ytr0221/BHA_Stirrer/Pictures/20160302_161547.jpg

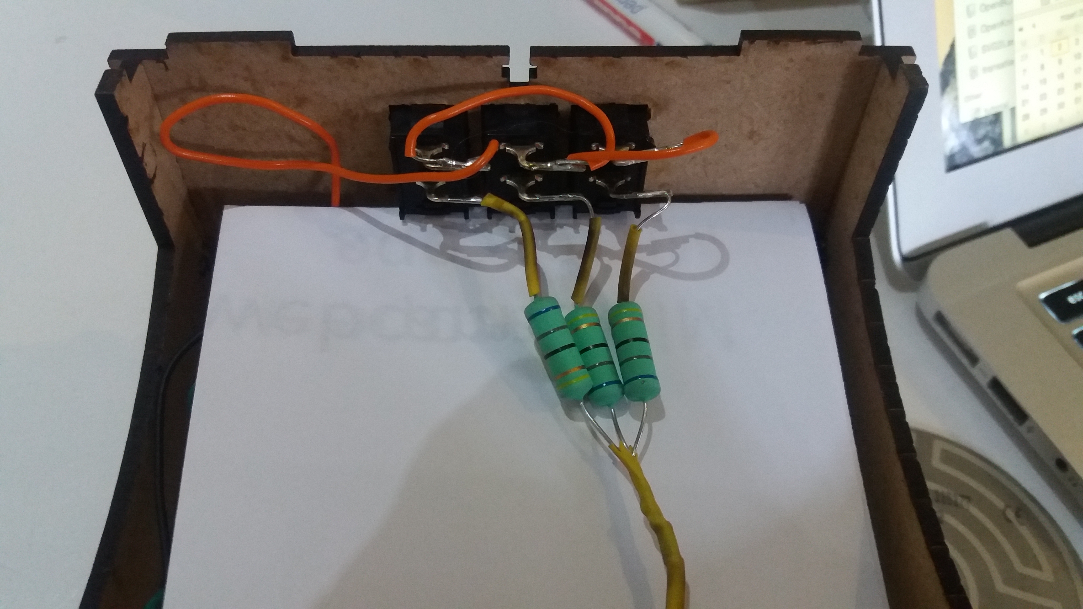
Pictures/20160302_161547.jpg
