ytr0221/BHA_Stirrer/Pictures/DSC_1296.JPG

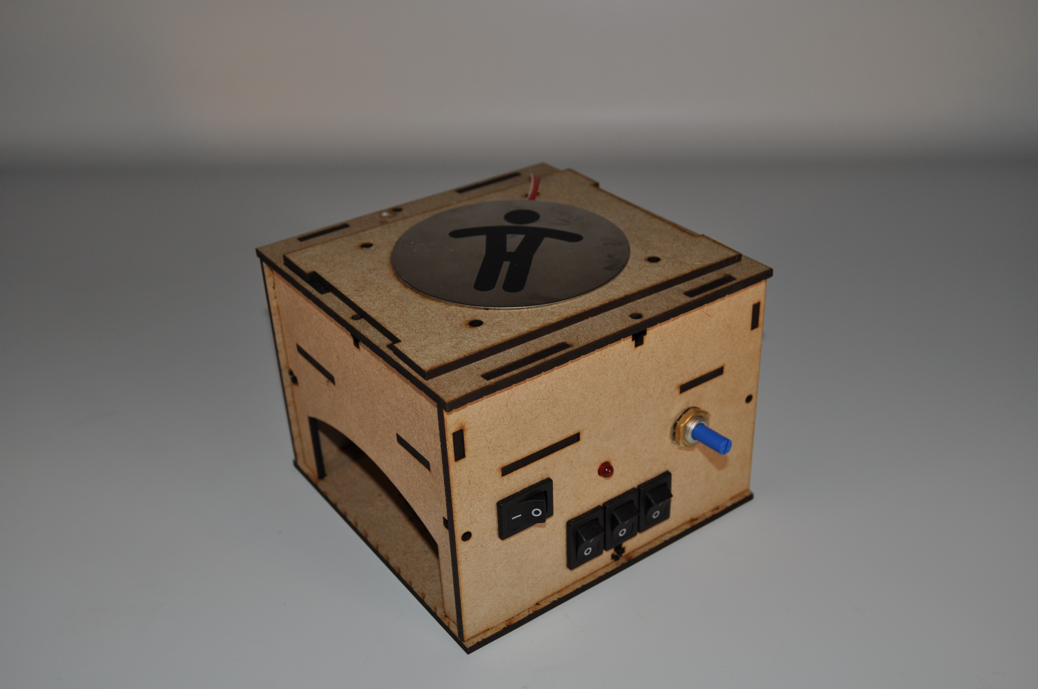
Pictures/DSC_1296.JPG
