ytr0221/BHA_Stirrer/Pictures/DSC_1297.JPG

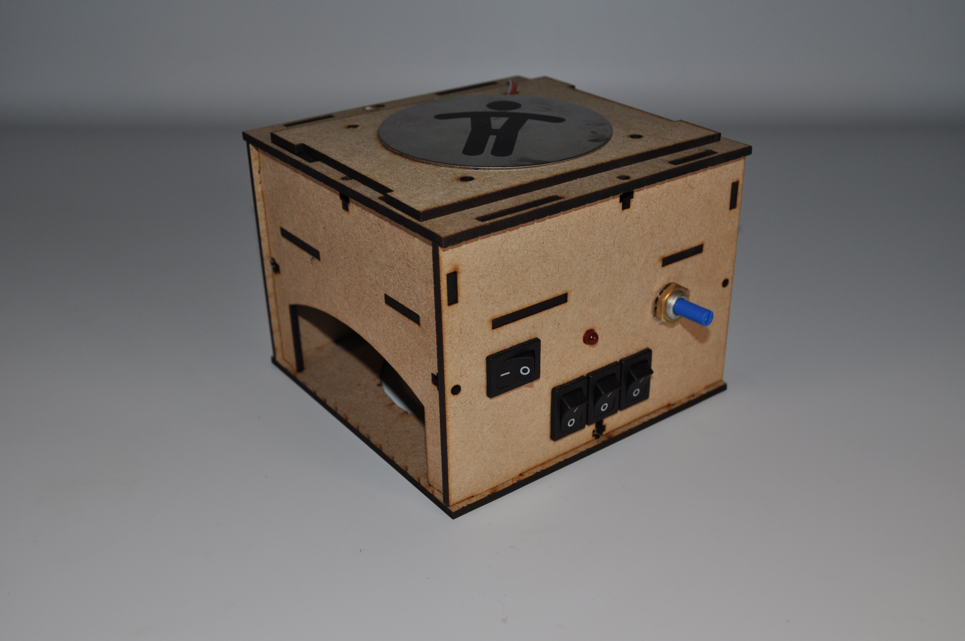
Pictures/DSC_1297.JPG
