ytr0221/BHA_Stirrer/Pictures/DSC_1299.JPG

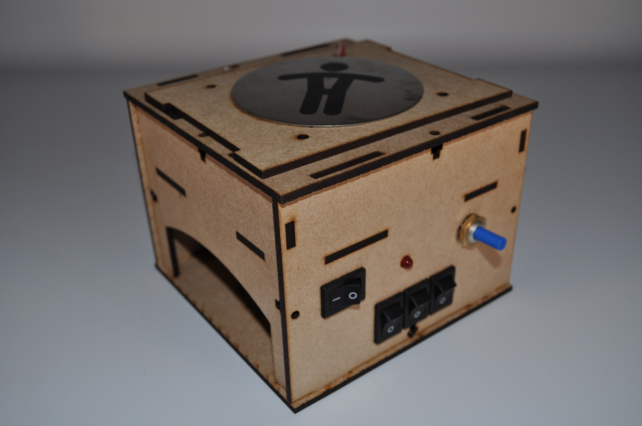
Pictures/DSC_1299.JPG
