ytr0221/BHA_Stirrer/Pictures/DSC_1300.JPG

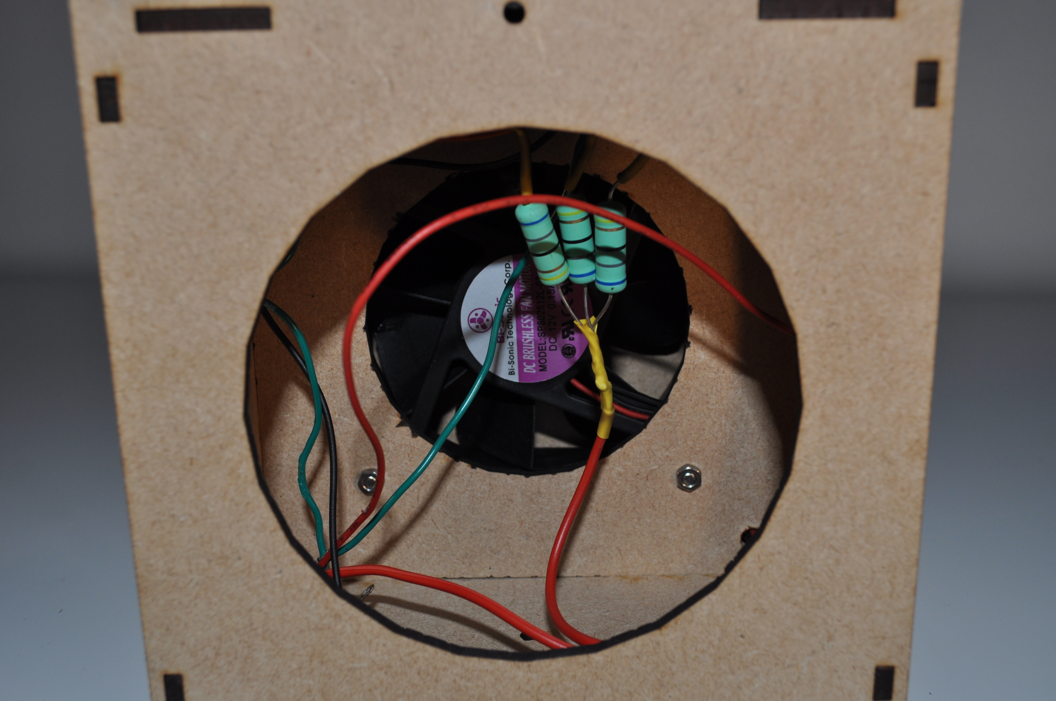
Pictures/DSC_1300.JPG
